SimplyYat/Wingboard/pcb/Wingboard PCB Back.png

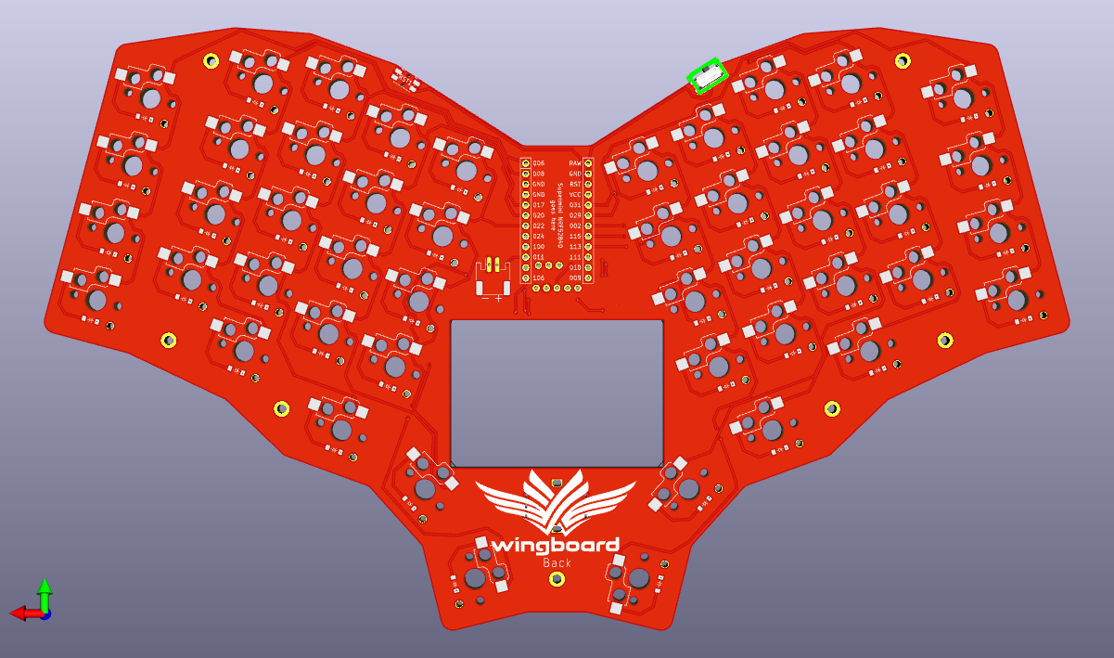
pcb/Wingboard PCB Back.png
